gpimblott/pico-dram-tester/firmware/sserif13.c

#include <stdint.h>
#include "st7789.h"

// Font size: 8
// Pixel height: 13
const uint8_t sserif13_widths[] = {
0,0,0,0,0,0,0,0,0,0,0,0,0,0,0,0,0,0,0,0,0,0,0,0,0,0,0,0,0,0,0,0,
3,3,5,7,6,8,6,2,3,3,4,6,3,3,3,5,6,6,6,6,6,6,6,6,6,6,3,3,6,6,6,6,
11,7,7,7,8,7,6,8,8,3,5,7,6,9,8,8,7,8,8,7,7,8,7,11,7,7,7,3,5,3,6,6,
3,6,6,6,6,6,3,6,6,2,2,6,2,8,6,6,6,6,3,5,3,6,6,8,5,5,5,4,2,4,7,3,
6,3,3,3,3,3,3,3,3,3,3,3,3,3,3,3,3,3,3,3,3,3,3,3,3,3,3,3,3,3,3,3,
3,3,6,6,6,6,2,6,3,9,4,6,6,3,8,6,4,6,3,3,3,6,6,3,3,3,4,6,8,8,8,6,
7,7,7,7,7,7,10,7,7,7,7,7,3,3,3,3,8,8,8,8,8,8,8,6,8,8,8,8,8,7,7,6,
6,6,6,6,6,6,10,6,6,6,6,6,2,4,4,4,6,6,6,6,6,6,6,6,6,6,6,6,6,5,6,5 };

const uint16_t sserif13_offsets[] = {
0,0,0,0,0,0,0,0,0,0,0,0,0,0,0,0,
0,0,0,0,0,0,0,0,0,0,0,0,0,0,0,0,
0,13,26,39,52,65,78,91,104,117,130,143,156,169,182,195,
208,221,234,247,260,273,286,299,312,325,338,351,364,377,390,403,
416,442,455,468,481,494,507,520,533,546,559,572,585,598,624,637,
650,663,676,689,702,715,728,741,767,780,793,806,819,832,845,858,
871,884,897,910,923,936,949,962,975,988,1001,1014,1027,1040,1053,1066,
1079,1092,1105,1118,1131,1144,1157,1170,1183,1196,1209,1222,1235,1248,1261,1274,
1287,1300,1313,1326,1339,1352,1365,1378,1391,1404,1417,1430,1443,1456,1469,1482,
1495,1508,1521,1534,1547,1560,1573,1586,1599,1612,1625,1638,1651,1664,1677,1690,
1703,1716,1729,1742,1755,1768,1781,1794,1807,1820,1846,1859,1872,1885,1898,1911,
1924,1937,1950,1963,1976,1989,2002,2015,2028,2041,2054,2067,2080,2093,2106,2119,
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
0x42,0x62,0x5c,0x00,0x00,0x00,0x00,0x42,0x42,0x42,0x42,0x7e,0x42,0x42,0x42,0x42,
0x00,0x00,0x00,0x00,0x02,0x02,0x02,0x02,0x02,0x02,0x02,0x02,0x02,0x00,0x00,0x00,
0x00,0x08,0x08,0x08,0x08,0x08,0x08,0x09,0x09,0x06,0x00,0x00,0x00,0x00,0x22,0x12,
0x0a,0x06,0x06,0x0a,0x12,0x22,0x42,0x00,0x00,0x00,0x00,0x02,0x02,0x02,0x02,0x02,
0x02,0x02,0x02,0x3e,0x00,0x00,0x00,0x00,0x00,0x00,0x82,0x00,0x82,0x00,0xc6,0x00,
0xc6,0x00,0xaa,0x00,0xaa,0x00,0x92,0x00,0x92,0x00,0x82,0x00,0x00,0x00,0x00,0x00,
0x00,0x00,0x42,0x46,0x46,0x4a,0x4a,0x52,0x62,0x62,0x42,0x00,0x00,0x00,0x00,0x3c,
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
const font_def_t sserif13 = { 256, 13, sserif13_widths, sserif13_offsets, sserif13_data };
