gpimblott/pico-dram-tester/firmware/sserif16.c

#include <stdint.h>
#include "st7789.h"

// Font size: 10
// Pixel height: 16
const uint8_t sserif16_widths[] = {
0,0,0,0,0,0,0,0,0,0,0,0,0,0,0,0,0,0,0,0,0,0,0,0,0,0,0,0,0,0,0,0,
3,3,5,7,7,12,9,3,4,4,5,7,3,4,3,4,7,7,7,7,7,7,7,7,7,7,3,3,7,7,7,7,
14,9,9,9,10,9,8,10,10,3,7,8,7,11,10,10,9,10,10,9,9,10,9,13,8,9,8,4,4,4,7,7,
4,8,8,7,8,8,3,8,7,3,3,7,3,11,7,8,8,8,4,7,3,7,7,9,6,7,6,5,3,5,9,4,
7,4,4,4,4,4,4,4,4,4,4,4,4,4,4,4,4,3,3,4,4,4,4,4,4,4,4,4,4,4,4,4,
3,3,7,7,7,7,3,7,4,8,5,7,7,4,8,7,4,7,4,4,4,7,7,3,4,4,5,7,9,9,9,7,
9,9,9,9,9,9,13,9,9,9,9,9,3,3,3,3,9,10,10,10,10,10,10,7,10,10,10,10,10,9,9,8,
8,8,8,8,8,8,13,7,8,8,8,8,3,3,3,3,8,7,8,8,8,8,8,7,8,7,7,7,7,7,8,7 };

const uint16_t sserif16_offsets[] = {
0,0,0,0,0,0,0,0,0,0,0,0,0,0,0,0,
0,0,0,0,0,0,0,0,0,0,0,0,0,0,0,0,
0,16,32,48,64,80,112,144,160,176,192,208,224,240,256,272,
288,304,320,336,352,368,384,400,416,432,448,464,480,496,512,528,
544,576,608,640,672,704,736,752,784,816,832,848,864,880,912,944,
976,1008,1040,1072,1104,1136,1168,1200,1232,1248,1280,1296,1312,1328,1344,1360,
1376,1392,1408,1424,1440,1456,1472,1488,1504,1520,1536,1552,1568,1584,1616,1632,
1648,1664,1680,1696,1712,1728,1744,1760,1792,1808,1824,1840,1856,1872,1888,1920,
1936,1952,1968,1984,2000,2016,2032,2048,2064,2080,2096,2112,2128,2144,2160,2176,
2192,2208,2224,2240,2256,2272,2288,2304,2320,2336,2352,2368,2384,2400,2416,2432,
2448,2464,2480,2496,2512,2528,2544,2560,2576,2592,2608,2624,2640,2656,2672,2688,
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
0x00,0x00,0x00,0x1c,0x22,0x22,0x20,0x10,0x08,0x08,0x08,0x00,0x08,0x00,0x00,0x00,
0x00,0x00,0x00,0x00,0xe0,0x01,0x18,0x06,0x04,0x08,0x04,0x08,0xc2,0x13,0x22,0x12,
0x22,0x12,0x22,0x11,0xc4,0x0e,0x04,0x00,0x18,0x0c,0xe0,0x03,0x00,0x00,0x00,0x00,
0x00,0x00,0x00,0x00,0x00,0x00,0x10,0x00,0x10,0x00,0x28,0x00,0x28,0x00,0x44,0x00,
0x44,0x00,0xfe,0x00,0x82,0x00,0x01,0x01,0x01,0x01,0x00,0x00,0x00,0x00,0x00,0x00,
0x00,0x00,0x00,0x00,0x00,0x00,0x7e,0x00,0x82,0x00,0x82,0x00,0x82,0x00,0x7e,0x00,
0x82,0x00,0x82,0x00,0x82,0x00,0x82,0x00,0x7e,0x00,0x00,0x00,0x00,0x00,0x00,0x00,
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
const font_def_t sserif16 = { 256, 16, sserif16_widths, sserif16_offsets, sserif16_data };
