gpimblott/pico-dram-tester/firmware/sserif20.c

#include <stdint.h>
#include "st7789.h"

// Font size: 12
// Pixel height: 20
const uint8_t sserif20_widths[] = {
0,0,0,0,0,0,0,0,0,0,0,0,0,0,0,0,0,0,0,0,0,0,0,0,0,0,0,0,0,0,0,0,
4,4,6,9,9,14,11,3,5,5,6,9,4,5,4,4,9,9,9,9,9,9,9,9,9,9,4,4,9,9,9,9,
16,11,11,11,12,11,10,13,12,5,8,10,9,13,11,12,10,12,12,11,9,12,11,15,11,11,10,4,4,4,7,9,
5,9,9,8,9,9,5,9,9,3,3,8,3,13,9,9,9,9,5,8,5,9,7,11,7,7,8,5,5,5,9,5,
9,5,5,5,5,5,5,5,5,5,5,5,5,5,5,5,5,4,4,5,5,5,5,5,5,5,5,5,5,5,5,5,
4,4,9,9,9,9,5,9,5,11,6,9,9,5,11,9,5,9,5,5,5,8,8,4,5,5,6,9,12,12,12,9,
11,11,11,11,11,11,16,11,11,11,11,11,5,5,5,5,12,11,12,12,12,12,12,9,12,12,12,12,12,11,10,10,
9,9,9,9,9,9,15,8,9,9,9,9,3,3,3,3,9,9,9,9,9,9,9,9,9,9,9,9,9,7,9,7 };

const uint16_t sserif20_offsets[] = {
0,0,0,0,0,0,0,0,0,0,0,0,0,0,0,0,
0,0,0,0,0,0,0,0,0,0,0,0,0,0,0,0,
0,20,40,60,100,140,180,220,240,260,280,300,340,360,380,400,
420,460,500,540,580,620,660,700,740,780,820,840,860,900,940,980,
1020,1060,1100,1140,1180,1220,1260,1300,1340,1380,1400,1420,1460,1500,1540,1580,
1620,1660,1700,1740,1780,1820,1860,1900,1940,1980,2020,2060,2080,2100,2120,2140,
2180,2200,2240,2280,2300,2340,2380,2400,2440,2480,2500,2520,2540,2560,2600,2640,
2680,2720,2760,2780,2800,2820,2860,2880,2920,2940,2960,2980,3000,3020,3040,3080,
3100,3140,3160,3180,3200,3220,3240,3260,3280,3300,3320,3340,3360,3380,3400,3420,
3440,3460,3480,3500,3520,3540,3560,3580,3600,3620,3640,3660,3680,3700,3720,3740,
3760,3780,3800,3840,3880,3920,3960,3980,4020,4040,4080,4100,4140,4180,4200,4240,
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
0x02,0x00,0xfe,0x00,0x00,0x00,0x00,0x00,0x00,0x00,0x00,0x00,0x00,0x00,0x00,0x00,
0x00,0x00,0x00,0x00,0x38,0x00,0x44,0x00,0x82,0x00,0x82,0x00,0x40,0x00,0x38,0x00,
0x40,0x00,0x80,0x00,0x82,0x00,0x82,0x00,0x44,0x00,0x38,0x00,0x00,0x00,0x00,0x00,
0x00,0x00,0x00,0x00,0x00,0x00,0x00,0x00,0x00,0x00,0x00,0x00,0x40,0x00,0x60,0x00,
0x60,0x00,0x50,0x00,0x48,0x00,0x48,0x00,0x44,0x00,0x42,0x00,0xfe,0x00,0x40,0x00,
0x40,0x00,0x40,0x00,0x00,0x00,0x00,0x00,0x00,0x00,0x00,0x00,0x00,0x00,0x00,0x00,
0x00,0x00,0x00,0x00,0xfe,0x00,0x02,0x00,0x02,0x00,0x02,0x00,0x3a,0x00,0x46,0x00,
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
const font_def_t sserif20 = { 256, 20, sserif20_widths, sserif20_offsets, sserif20_data };
