gpimblott/pico-dram-tester/firmware/icons.c

// This file contains the definitions for all icon data.
#include "gui.h"
#include <stdint.h>

// --- check_icon ---
uint16_t check_icon_palette[] = { 0x8000, 0x0400, 0x8410, 0x07E0, 0x0000, 0x0000, 0x0000, 0x0000, 0x0000, 0x0000, 0x0000, 0x0000, 0x0000, 0x0000, 0x0000, 0x0000 };
const uint8_t check_icon_image[] = {
0x44, 0x44, 0x44, 0x44, 0x44, 0x44, 0x44, 0x44, 0x44, 0x44, 0x44, 0x44, 0x44, 0x44, 0x44, 0x44,
0x44, 0x44, 0x44, 0x44, 0x44, 0x44, 0x44, 0x44, 0x44, 0x44, 0x44, 0x44, 0x44, 0x44, 0x44, 0x44,
0x44, 0x44, 0x44, 0x44, 0x44, 0x44, 0x44, 0x44, 0x44, 0x44, 0x44, 0x44, 0x44, 0x44, 0x44, 0x44,
0x44, 0x44, 0x44, 0x44, 0x42, 0x22, 0x44, 0x44, 0x44, 0x44, 0x44, 0x44, 0x44, 0x44, 0x44, 0x44,
0x44, 0x44, 0x44, 0x44, 0x22, 0x22, 0x24, 0x44, 0x44, 0x44, 0x44, 0x44, 0x44, 0x44, 0x44, 0x44,
0x44, 0x44, 0x44, 0x40, 0x00, 0x22, 0x22, 0x44, 0x44, 0x44, 0x44, 0x44, 0x44, 0x44, 0x44, 0x44,
0x44, 0x44, 0x44, 0x01, 0x10, 0x02, 0x22, 0x24, 0x44, 0x44, 0x44, 0x44, 0x44, 0x44, 0x44, 0x44,
0x44, 0x44, 0x43, 0x11, 0x11, 0x00, 0x22, 0x22, 0x44, 0x44, 0x44, 0x44, 0x44, 0x44, 0x44, 0x44,
0x44, 0x44, 0x31, 0x11, 0x11, 0x10, 0x02, 0x22, 0x24, 0x44, 0x44, 0x44, 0x44, 0x44, 0x44, 0x44,
0x44, 0x44, 0x31, 0x11, 0x11, 0x11, 0x00, 0x22, 0x22, 0x44, 0x44, 0x44, 0x44, 0x44, 0x44, 0x44,
0x44, 0x44, 0x31, 0x11, 0x11, 0x11, 0x10, 0x02, 0x22, 0x24, 0x44, 0x44, 0x44, 0x44, 0x44, 0x44,
0x44, 0x44, 0x31, 0x11, 0x11, 0x11, 0x11, 0x00, 0x22, 0x22, 0x44, 0x44, 0x44, 0x44, 0x44, 0x44,
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
0xff, 0x03, 0xe0, 0x1f,
0xfe, 0x07, 0xf0, 0x3f,
0xff, 0x8f, 0xf8, 0x7f,
0xff, 0xff, 0xfc, 0xff,
0xff, 0xff, 0xff, 0xff,
0xff, 0xff, 0xff, 0xff,
0xff, 0xff, 0xff, 0xff,
0xff, 0xff, 0xff, 0xff,
0xff, 0xff, 0xff, 0xff
};
const ico_def_t x_icon = { 32, 34, x_icon_palette, x_icon_image, x_icon_mask };
