gpimblott/pico-dram-tester/firmware/rtc_image.h

const uint16_t image_data[] = {
0xd7bf, 0xd7bf, 0xd7bf, 0xd7bf, 0xd7bf, 0xd7bf, 0xd7bf, 0xd7bf,
0xd7bf, 0xd7bf, 0xd7bf, 0xd7bf, 0xd7bf, 0xd7bf, 0xd7bf, 0xd7bf,
0xd7bf, 0xd7bf, 0xd7bf, 0xd7bf, 0xd7bf, 0xd7bf, 0xd7bf, 0xd7bf,
0xd7bf, 0xd7bf, 0xd7bf, 0xd7bf, 0xd7bf, 0xd7bf, 0xd7bf, 0xd7bf,
0xd7bf, 0xd7bf, 0xd7bf, 0xd7bf, 0xd7bf, 0xd7bf, 0xd7bf, 0xd7bf,
0xd7bf, 0xd7bf, 0xd7bf, 0xd7bf, 0xd7bf, 0xd7bf, 0xd7bf, 0xd7bf,
0xd7bf, 0xd7bf, 0xd7bf, 0xd7bf, 0xd7bf, 0xd7bf, 0xd7bf, 0xd7bf,
0xd7bf, 0xd7bf, 0xd7bf, 0xd7bf, 0xd7bf, 0xd7bf, 0xd7bf, 0xd7bf,
0xd7bf, 0xd7bf, 0xd7bf, 0xd7df, 0xd7ff, 0xd7df, 0xcf9f, 0xcf7f,
0xdfff, 0xcfdf, 0xd7df, 0xc73f, 0xc73f, 0xc6df, 0xb63f, 0x9d3f,
0x845f, 0x7bdf, 0x737f, 0x633f, 0x6b5f, 0x6b5f, 0x6b5f, 0x6b5f,
0x6b5f, 0x6b5f, 0x635f, 0x637f, 0x637f, 0x639e, 0x639e, 0x639e,
0x637f, 0x635f, 0x635f, 0x635f, 0x635f, 0x635f, 0x635f, 0x635f,
0x635f, 0x635f, 0x637f, 0x637f, 0x6b7f, 0x6b7f, 0x6b7f, 0x6b7f,
0x6b5f, 0x6b5f, 0x6b5f, 0x6b5f, 0x6b5f, 0x6b5f, 0x6b5f, 0x6b5f,
0x6b5f, 0x6b5f, 0x6b5f, 0x6b5f, 0x6b5f, 0x6b5f, 0x6b5f, 0x6b7f,
0x6b7f, 0x6b7f, 0x6b5f, 0x6b5f, 0x6b5f, 0x6b5f, 0x6b7f, 0x6b7f,
0x637f, 0x635f, 0x635f, 0x635f, 0x6b5f, 0x6b5f, 0x6b5f, 0x6b5f,
0x6b5f, 0x6b5f, 0x6b5f, 0x6b5f, 0x6b5f, 0x6b5f, 0x6b5f, 0x6b5f,
0x6b5f, 0x6b5f, 0x6b5f, 0x6b5f, 0x6b5f, 0x6b5f, 0x6b5f, 0x6b5f,
0x6b5f, 0x6b5f, 0x6b5f, 0x6b5f, 0x6b5f, 0x6b5f, 0x6b5f, 0x6b5f,
0x6b5f, 0x6b5f, 0x6b5f, 0x6b5f, 0x6b5f, 0x6b5f, 0x6b5f, 0x6b5f,
0x6b5f, 0x6b5f, 0x6b5f, 0x6b5f, 0x6b7f, 0x6b9f, 0x6b9f, 0x6b9f,
0x6b7f, 0x6b5f, 0x637f, 0x637f, 0x637f, 0x637f, 0x637f, 0x637f,
0x6b5f, 0x6b5f, 0x6b5f, 0x6b5f, 0x6b5f, 0x6b5f, 0x6b5f, 0x6b7f,
0x6b7f, 0x6b9f, 0x6b9f, 0x6b9f, 0x6b9f, 0x7bff, 0x8c7f, 0x94df,
0xa5bf, 0xbe9f, 0xc6ff, 0xbeff, 0xd79f, 0xcf9f, 0xcfbf, 0xcfdf,
0xd7bf, 0xd7bf, 0xdfbf, 0xd79f, 0xd7be, 0xd7de, 0xd7de, 0xd7bf,
0xd7bf, 0xd7bf, 0xd7bf, 0xd7bf, 0xd7bf, 0xd7bf, 0xd7bf, 0xd7bf,
0xd7bf, 0xd7bf, 0xd7bf, 0xd7bf, 0xd7bf, 0xd7bf, 0xd7bf, 0xd7bf,
0xd7bf, 0xd7bf, 0xd7bf, 0xd7bf, 0xd7bf, 0xd7bf, 0xd7bf, 0xd7bf,
0xd7bf, 0xd7bf, 0xd7bf, 0xd7bf, 0xd7bf, 0xd7bf, 0xd7bf, 0xd7bf,
0xd7bf, 0xd7bf, 0xd7bf, 0xd7bf, 0xd7bf, 0xd7bf, 0xd7bf, 0xd7bf,
0xd7bf, 0xd7bf, 0xd7bf, 0xd7bf, 0xd7bf, 0xd7bf, 0xd7bf, 0xd7bf,
0xd7bf, 0xd7bf, 0xd7bf, 0xd7bf, 0xd7bf, 0xd7bf, 0xd7bf, 0xd7bf,
0xd7bf, 0xd7bf, 0xd7bf, 0xd7bf, 0xd7bf, 0xd7bf, 0xd7bf, 0xd7bf,
0xd7bf, 0xd7bf, 0xd7bf, 0xd7bf, 0xd7bf, 0xd7bf, 0xd7bf, 0xd7bf,
0xd7bf, 0xd7bf, 0xd7bf, 0xd7bf, 0xd7bf, 0xd7bf, 0xd7bf, 0xd7bf,
0xd7bf, 0xd7bf, 0xd7df, 0xd7df, 0xd7bf, 0xcf9f, 0xcf7f, 0xcf7f,
0xcf7f, 0xc73f, 0xb67f, 0x84fc, 0x63da, 0x4af8, 0x3a17, 0x3a18,
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
};
