gpimblott/pico-dram-tester/firmware/sserif13.h

#ifndef SSERIF13_H
#define SSERIF13_H

extern const uint8_t sserif13_widths[];
extern const uint16_t sserif13_offsets[];
extern const uint8_t sserif13_data[];
extern const font_def_t sserif13;

#endif
