gpimblott/pico-dram-tester/firmware/sserif16.h

#ifndef SSERIF16_H
#define SSERIF16_H

extern const uint8_t sserif16_widths[];
extern const uint16_t sserif16_offseets[];
extern const uint8_t sserif16_data[];
extern const font_def_t sserif16;


#endif
