gpimblott/pico-dram-tester/firmware/sserif20.h

#ifndef SSERIF20_H
#define SSERIF20_H

extern const uint8_t sserif20_widths[];
extern const uint16_t sserif20_offsets[];
extern const uint8_t sserif20_data[];
extern const font_def_t sserif20;

#endif
