gpimblott/pico-dram-tester/firmware/pio_patcher.h

#ifndef pio_patcher_h
#define pio_patcher_h

void set_current_pio_program(const struct pio_program *prog);
struct pio_program *get_current_pio_program();
void pio_patch_delays(const uint8_t *delays, uint8_t length);


#endif
