gpimblott/pico-dram-tester/firmware/widgets16.h

// Pixel height: 16
const uint8_t widgets16_widths[] = {0, 13, 9, 9};
const uint16_t widgets16_offsets[] = {0, 0, 32, 64, 96};
const uint8_t widgets16_data[] = {
0x00,0x00,
0x00,0x00,
0x00,0x00,
0x03,0x06,
0x07,0x07,
0x8e,0x03,
0xdc,0x01,
0xf8,0x00,
0x70,0x00,
0xf8,0x00,
0xdc,0x01,
0x8e,0x03,
0x07,0x07,
0x03,0x06,
0x00,0x00,
0x00,0x00,

0x00,0x00,
0x00,0x00,
0x00,0x00,
0x00,0x00,
0x00,0x00,
0xff,0x01,
0xfe,0x00,
0x7c,0x00,
0x38,0x00,
0x10,0x00,
0x00,0x00,
0x00,0x00,
0x00,0x00,
0x00,0x00,
0x00,0x00,
0x00,0x00,

0x00,0x00,
0x00,0x00,
0x00,0x00,
0x00,0x00,
0x00,0x00,
0x10,0x00,
0x38,0x00,
0x7c,0x00,
0xfe,0x00,
0xff,0x01,
0x00,0x00,
0x00,0x00,
0x00,0x00,
0x00,0x00,
0x00,0x00,
0x00,0x00,




};
const font_def_t widgets16 = { 4, 16, widgets16_widths, widgets16_offsets, widgets16_data };
